jaku2019/ETH32/photos/ETH32_photo (2).png

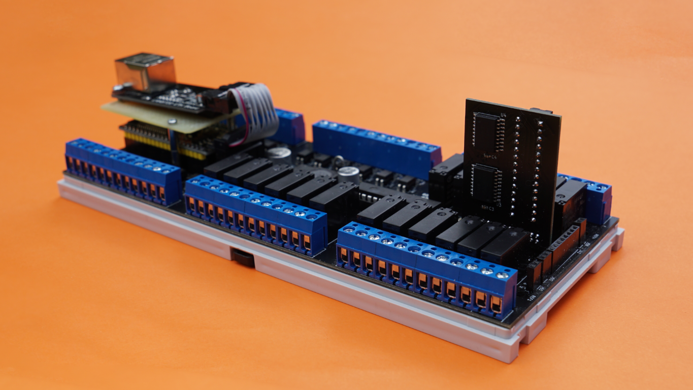
photos/ETH32_photo (2).png
