jaku2019/ETH32/photos/ETH32_photo (6).png

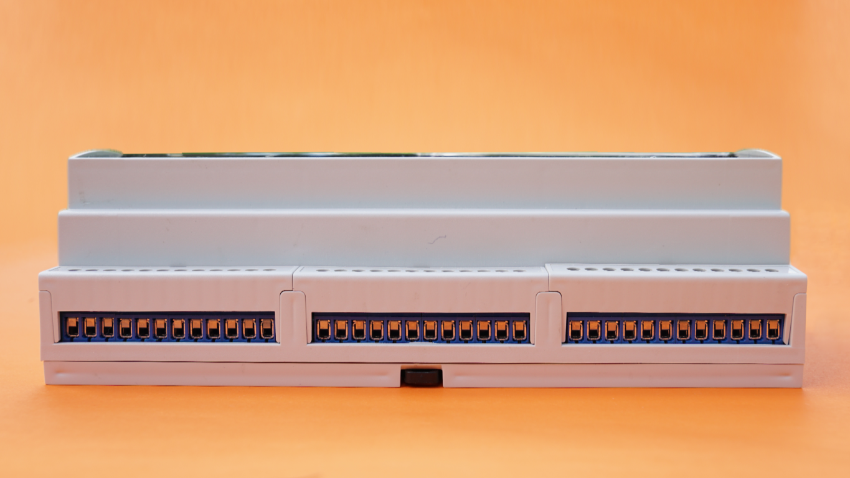
photos/ETH32_photo (6).png
