jaku2019/ETH32/photos/ETH32_photo (7).png

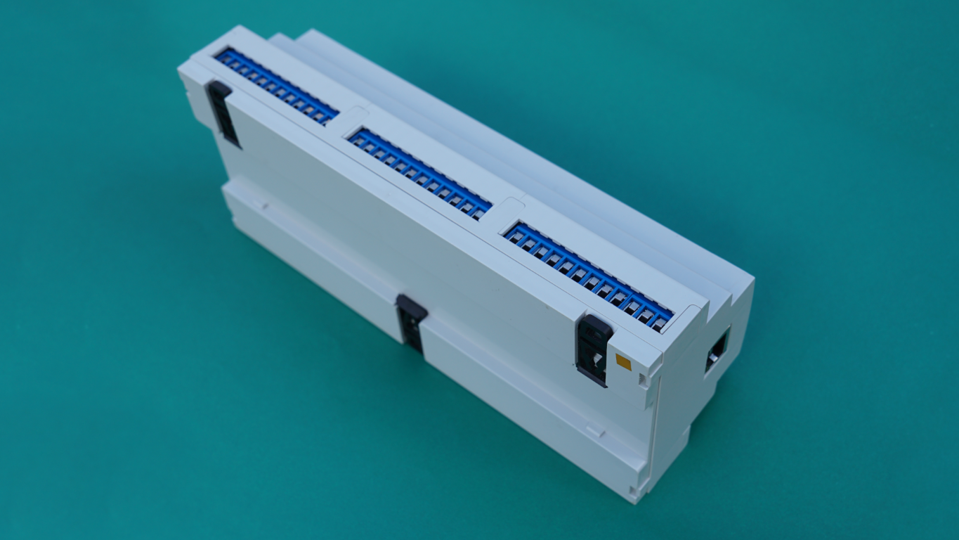
photos/ETH32_photo (7).png
