jaku2019/ETH32/photos/ETH32_photo (8).JPG

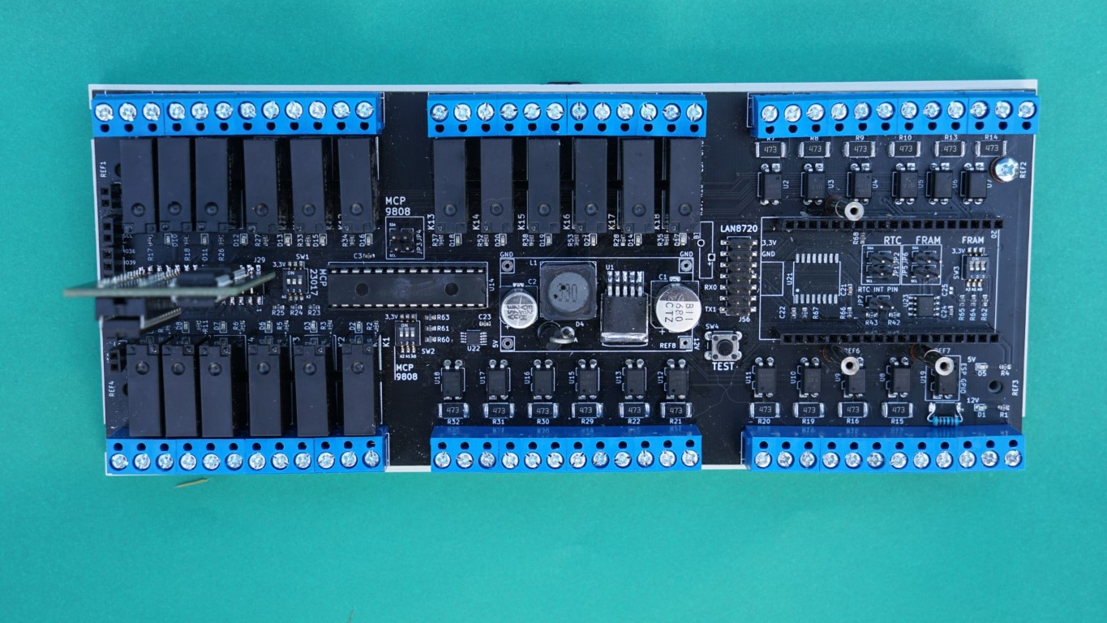
photos/ETH32_photo (8).JPG
